Other-Project/PeiP2-Distribuino/decoupes et impressions/tube 10 centimes (1).stl

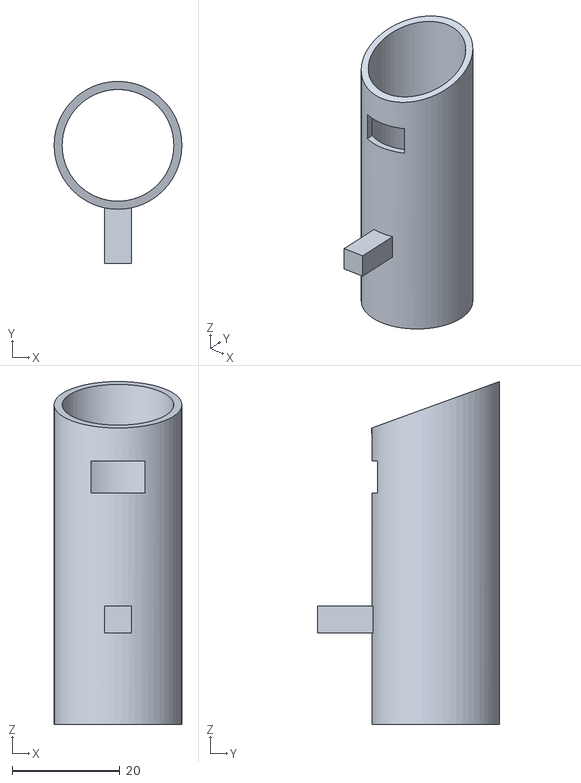
[picture p36: CAD file, 2023-03-15]
decoupes et impressions/tube 10 centimes (1).stl
23.8 x 33.8 x 63.7
