Other-Project/PeiP2-Distribuino/decoupes et impressions/support 1 euro (2).stl

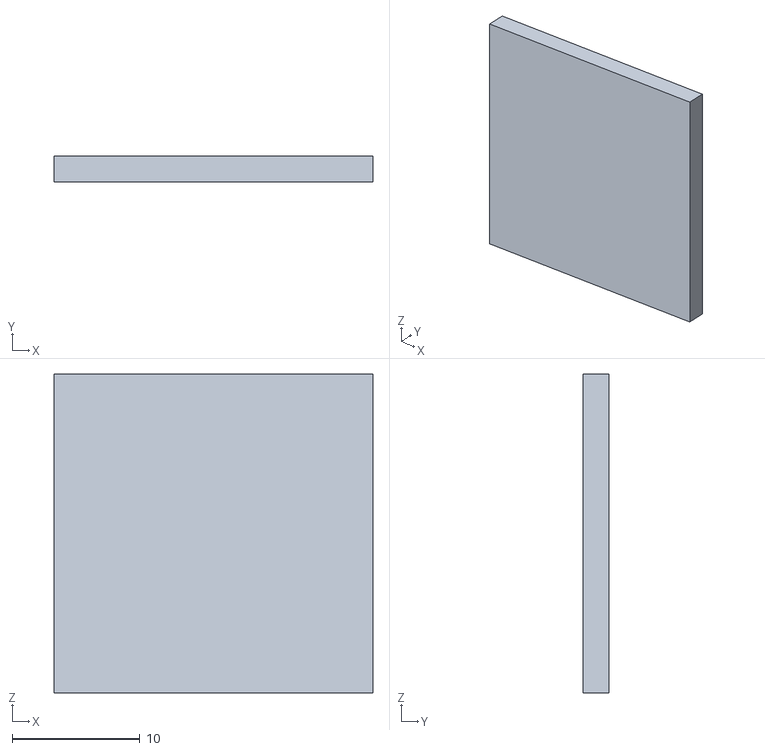
[picture p37: CAD file, 2023-03-15]
decoupes et impressions/support 1 euro (2).stl
25.0 x 2.00 x 25.0
