Other-Project/PeiP2-Distribuino/decoupes et impressions/support 10 centimes (2).stl

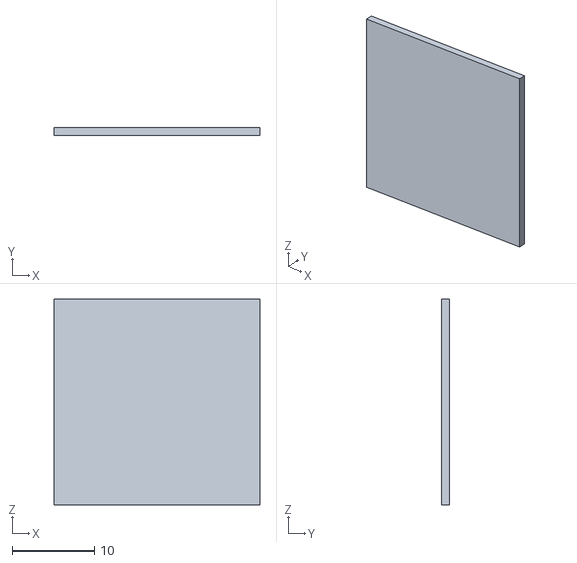
[picture p38: CAD file, 2023-03-15]
decoupes et impressions/support 10 centimes (2).stl
25.0 x 1.00 x 25.0
