Other-Project/PeiP2-Distribuino/decoupes et impressions/guide 2 centimes (1).stl

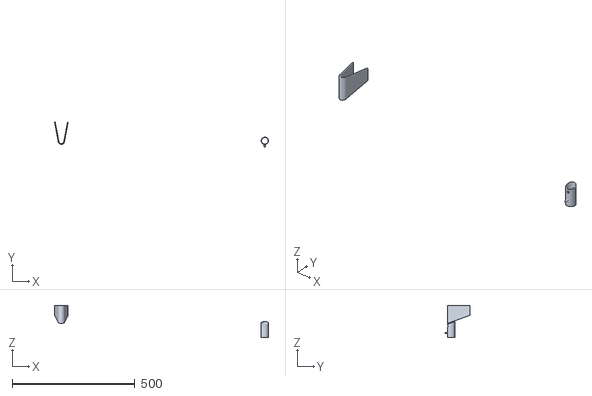
[picture p39: CAD file, 2023-03-15]
decoupes et impressions/guide 2 centimes (1).stl
872.3 x 101.1 x 132.0
