Other-Project/PeiP2-Distribuino/decoupes et impressions/Systeme de trie des pièces partie haute.stl

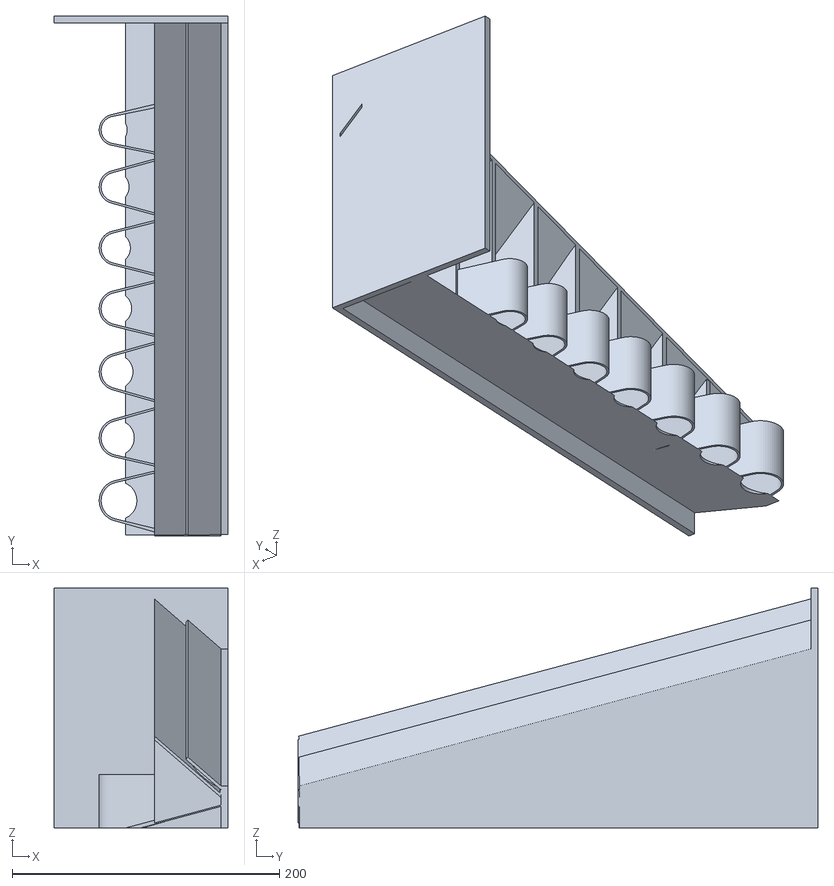
[picture p40: CAD file, 2023-01-19]
decoupes et impressions/Systeme de trie des pièces partie haute.stl
130.0 x 388.9 x 179.5
