Other-Project/PeiP2-Distribuino/decoupes et impressions/Système de trie des pièces.stl

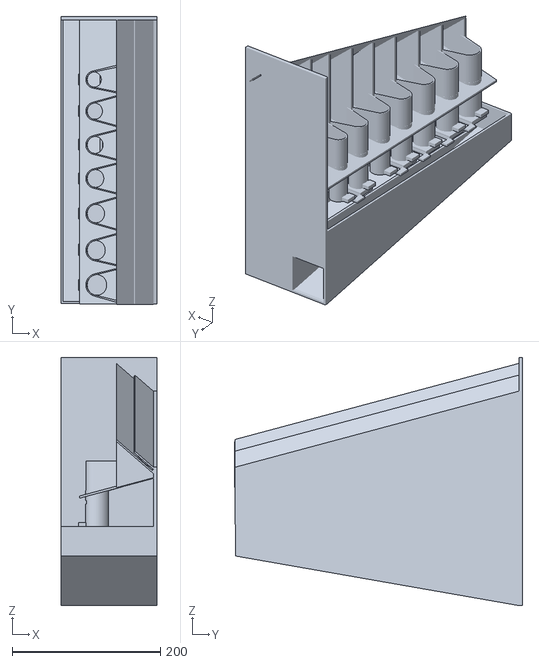
[picture p41: CAD file, 2023-01-19]
decoupes et impressions/Système de trie des pièces.stl
130.0 x 388.9 x 335.0
