Other-Project/PeiP2-Distribuino/decoupes et impressions/Système de trie des pièces partie basse.stl

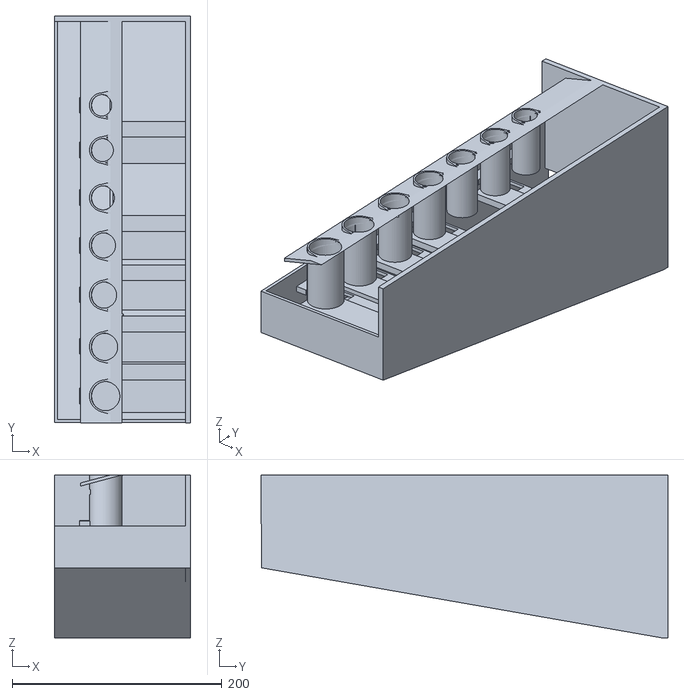
[picture p42: CAD file, 2023-01-19]
decoupes et impressions/Système de trie des pièces partie basse.stl
130.0 x 388.0 x 155.5
